gheleguen/remorque_atelier/docs/pictures/6.png

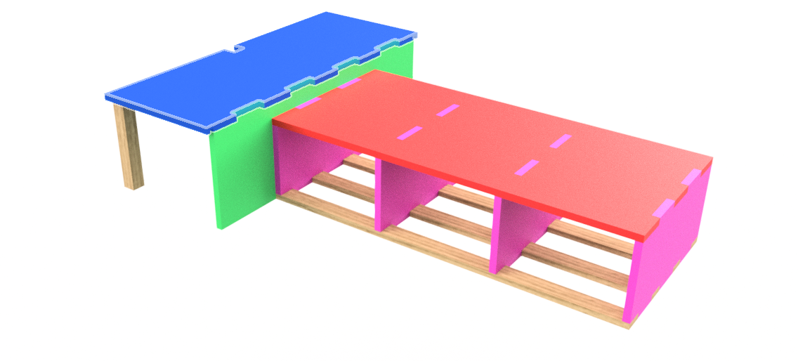
docs/pictures/6.png
