gheleguen/remorque_atelier/docs/pictures/AM3-5.jpg

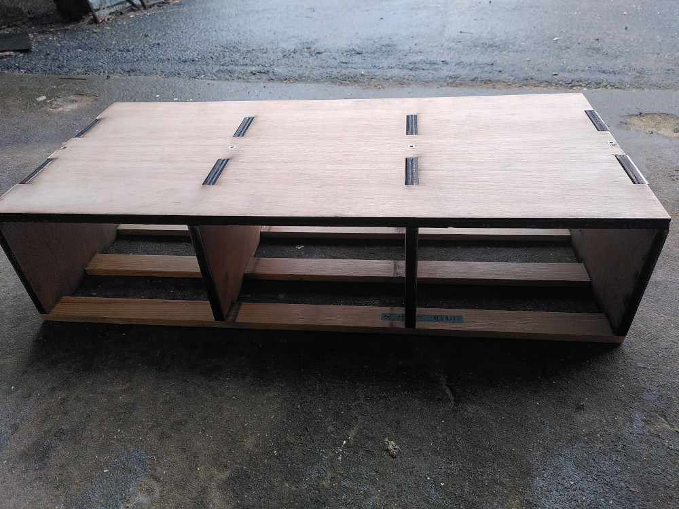
docs/pictures/AM3-5.jpg
