gheleguen/remorque_atelier/docs/pictures/E1.png

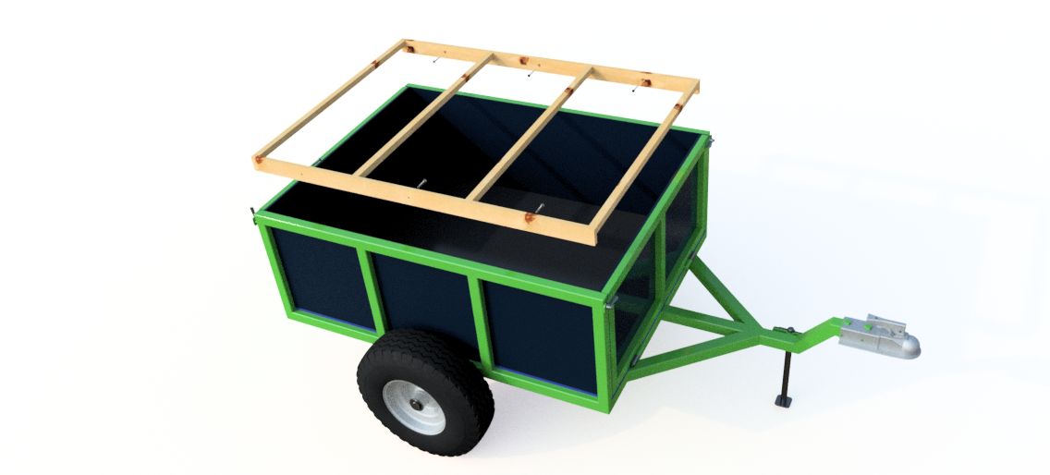
docs/pictures/E1.png
