gheleguen/remorque_atelier/docs/pictures/E15.png

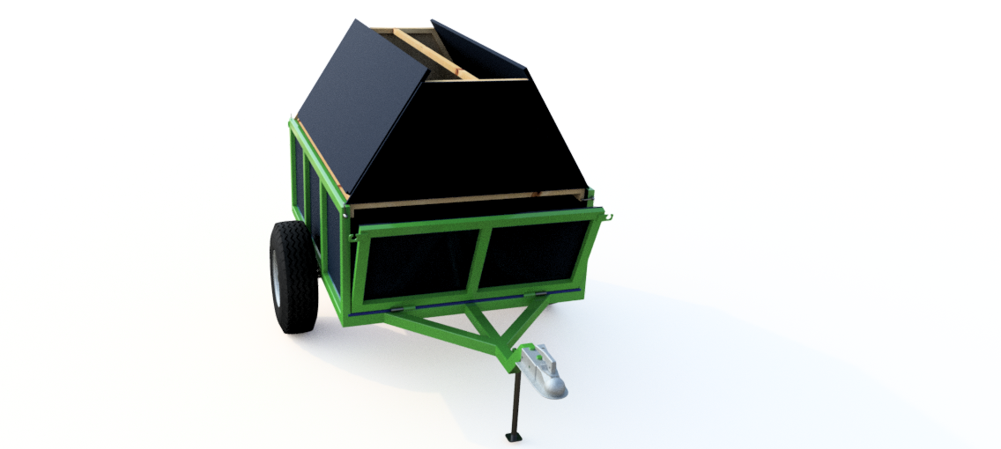
docs/pictures/E15.png
